machtmu/4-in-power-management/kicad/models/CONN-SMD_S4B-XH-SM4-TB-LF-SN.step

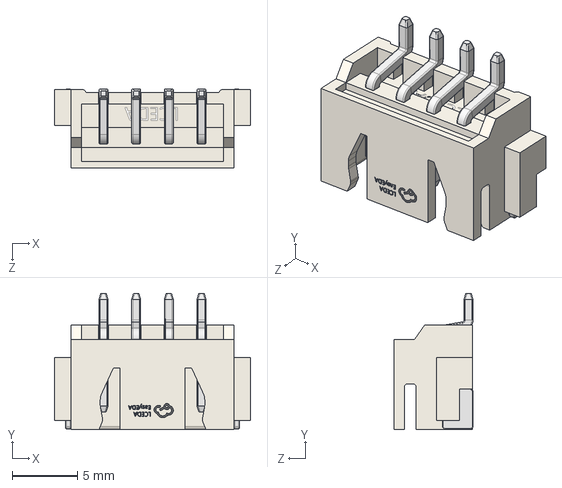
[picture p17: CAD file, 2025-09-12]
kicad/models/CONN-SMD_S4B-XH-SM4-TB-LF-SN.step
15.0 x 10.4 x 6.06 mm
