machtmu/4-in-power-management/kicad/models/F1206.step

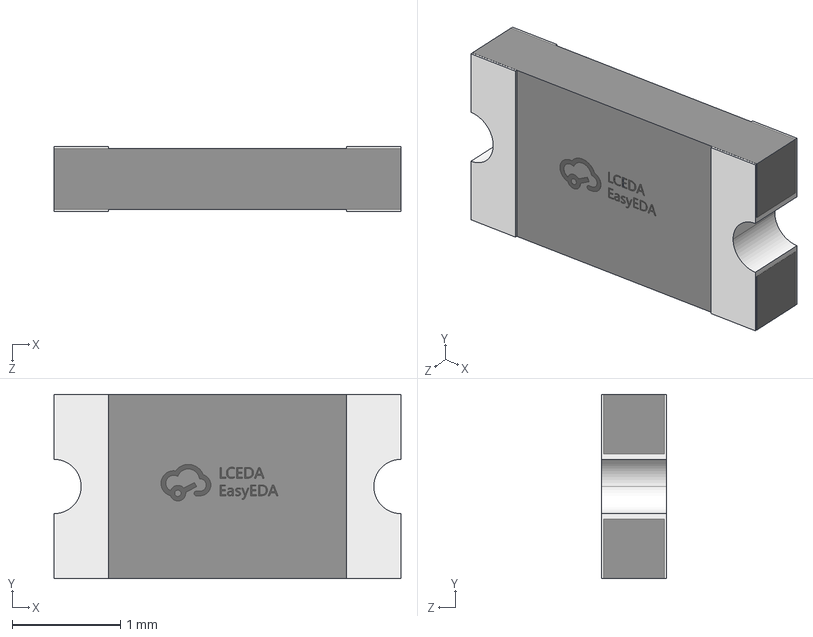
[picture p18: CAD file, 2025-09-12]
kicad/models/F1206.step
3.20 x 1.70 x 0.6 mm
