machtmu/4-in-power-management/kicad/models/SOT-223-3_L6.5-W3.4-P2.30-LS7.0-BR.step

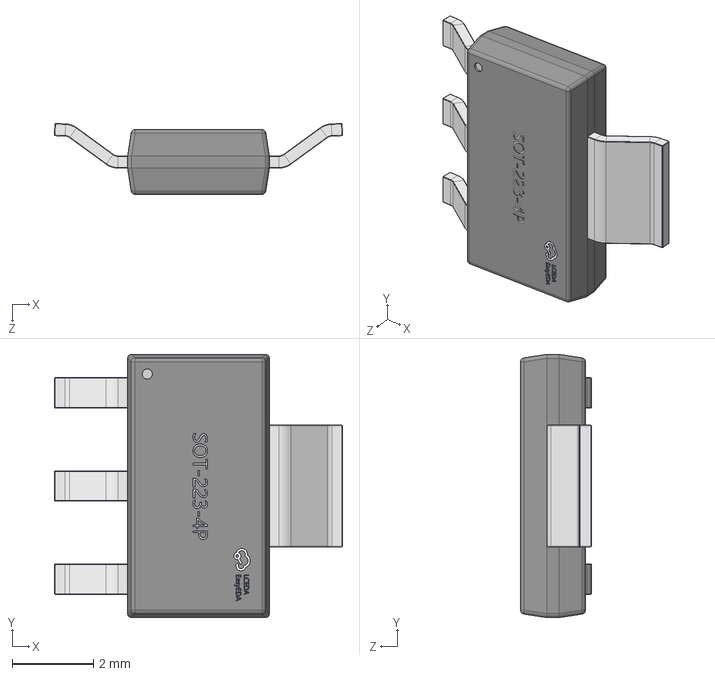
[picture p19: CAD file, 2025-09-12]
kicad/models/SOT-223-3_L6.5-W3.4-P2.30-LS7.0-BR.step
7.11 x 6.50 x 1.75 mm
