machtmu/4-in-power-management/kicad/models/CONN-TH_XT30PW-M.step

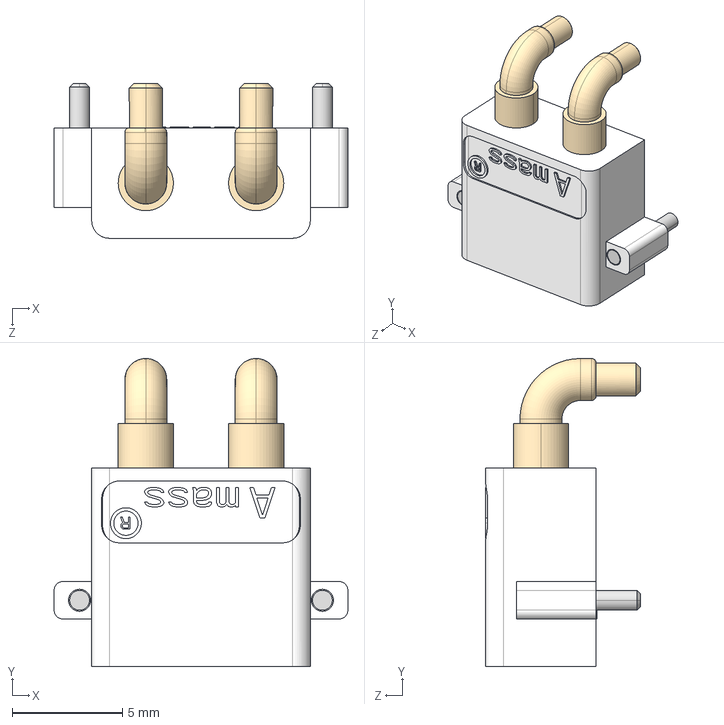
[picture p20: CAD file, 2025-09-12]
kicad/models/CONN-TH_XT30PW-M.step
13.3 x 13.9 x 7.00 mm
