machtmu/4-in-power-management/kicad/models/SMD_RH-5015.step

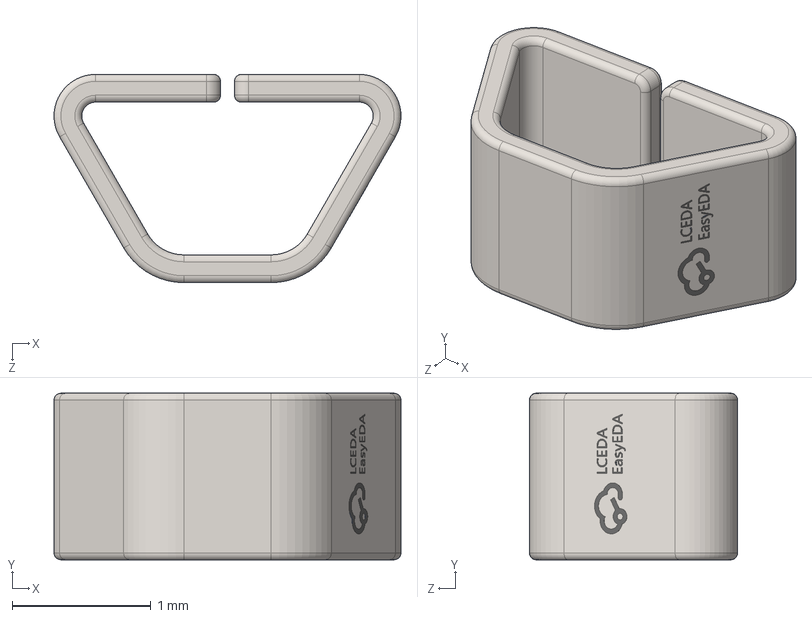
[picture p21: CAD file, 2025-09-12]
kicad/models/SMD_RH-5015.step
2.50 x 1.20 x 1.50 mm
