machtmu/4-in-power-management/kicad/models/SOT-23-6_L2.9-W1.6-P0.95-LS2.8-BL.step

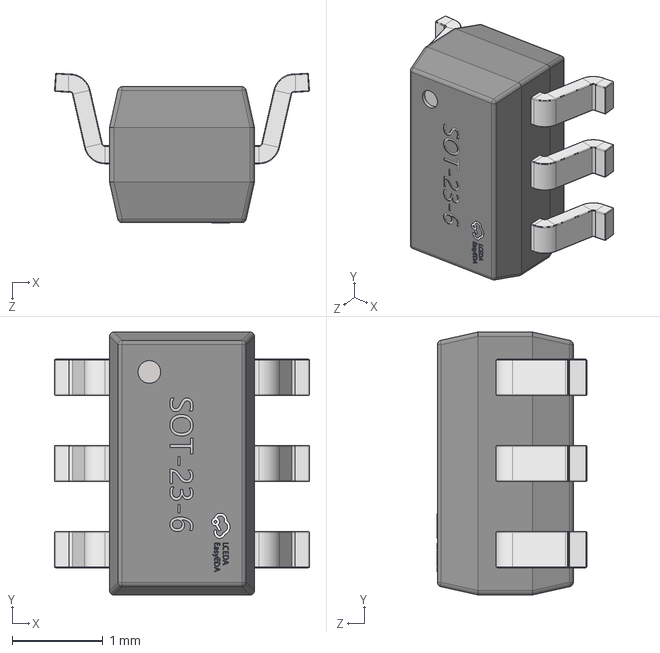
[picture p22: CAD file, 2025-09-12]
kicad/models/SOT-23-6_L2.9-W1.6-P0.95-LS2.8-BL.step
2.81 x 2.90 x 1.65 mm
