machtmu/4-in-power-management/kicad/models/CRYSTAL-SMD_4P-L3.2-W2.5-BL.step

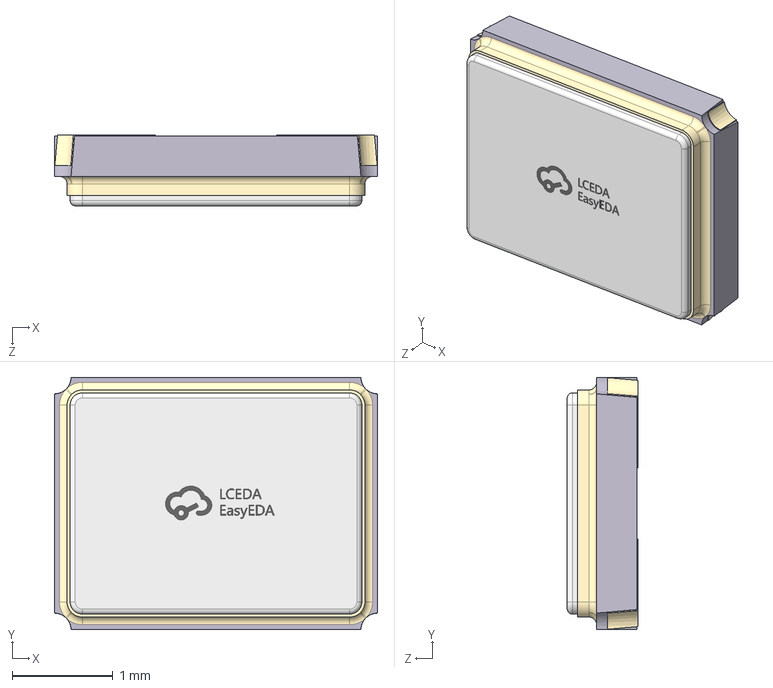
[picture p23: CAD file, 2025-09-12]
kicad/models/CRYSTAL-SMD_4P-L3.2-W2.5-BL.step
3.20 x 2.50 x 0.701 mm
