machtmu/4-in-power-management/kicad/models/IND-SMD_L5.4-W5.2_SLO0530H6R8MTT.step

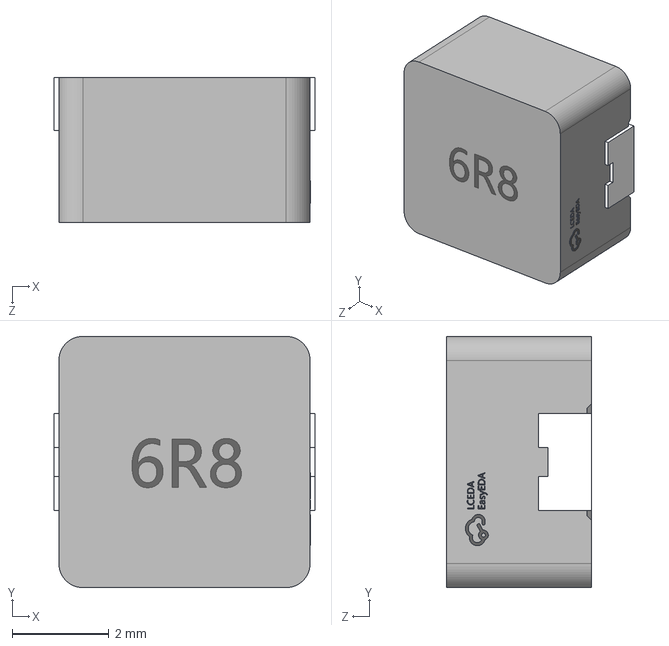
[picture p24: CAD file, 2025-09-12]
kicad/models/IND-SMD_L5.4-W5.2_SLO0530H6R8MTT.step
5.40 x 5.20 x 3.01 mm
